oliviasculley/busy-light/busy-light-1.0.0/busy-light-rev-1.0.0.png

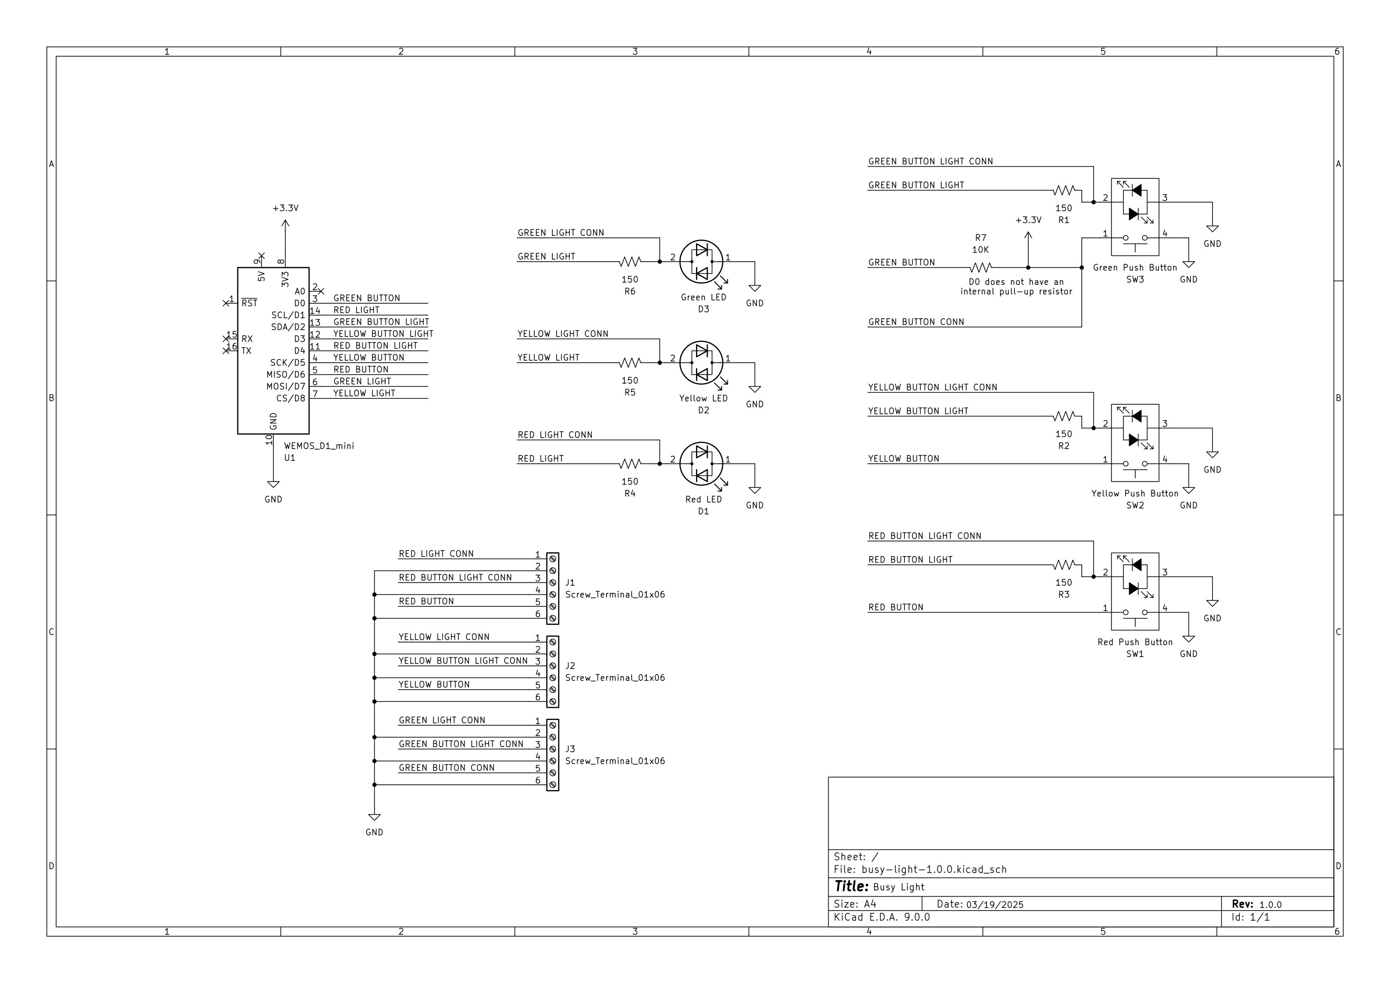
busy-light-1.0.0/busy-light-rev-1.0.0.png
